M-Mrk/BlitzPong/pcb/controller/power.kicad_sch

## KiCad design pcb/controller/power.kicad_sch (2026-06-27)

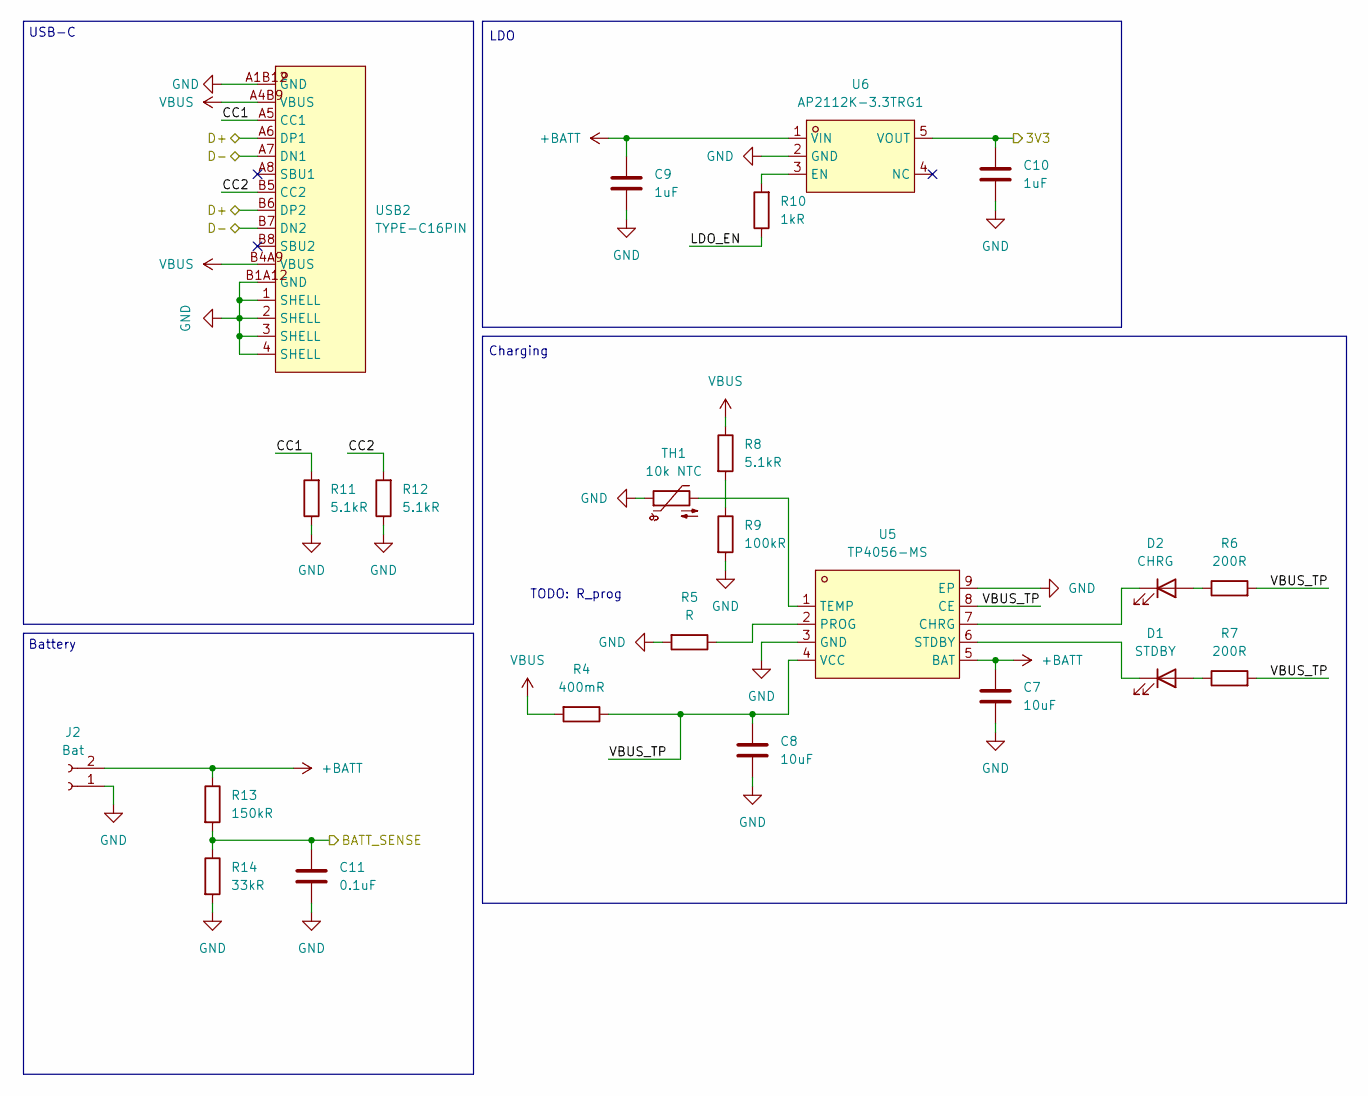
[picture p7: schematic power.kicad_sch]

Parts:
C7, C8: 10uF
C9, C10: 1uF
C11: 0.1uF
D1: STDBY; LED_0603_1608Metric; LCSC Part C51933293
D2: CHRG; LED_0603_1608Metric; LCSC Part C19712529
J2: Bat
R4: 400mR; R_2512_6332Metric; LCSC Part C49164929
R5: R
R6, R7: 200R
R8, R11, R12: 5.1kR
R9: 100kR
R10: 1kR
R13: 150kR
R14: 33kR
TH1: 10k NTC; SolderWire-0.1sqmm_1x02_P3.6mm_D0.4mm_OD1mm; LCSC Part C52204608
U5: TP4056-MS; SOP-8_L4.9-W3.9-P1.27-LS6.0-TL-EP; MPN TP4056-MS; LCSC Part C7473158
U6: AP2112K-3.3TRG1; SOT-23-5_L2.9-W1.6-P0.95-LS2.7-BR; MPN AP2112K-3.3TRG1(MS); LCSC Part C22365427
USB2: TYPE-C16PIN; USB-C-SMD_TYPE-C16PIN; MPN TYPE-C16PIN; LCSC Part C393939

Connections:
3V3: C10.1, U6.5 (VOUT)
+BATT: C7.1, C9.1, J2.2, R13.1, U5.5 (BAT), U6.1 (VIN)
BATT_SENSE: C11.1, R13.2, R14.1
CC1: R11.2, USB2.A5 (CC1)
CC2: R12.2, USB2.B5 (CC2)
D+: USB2.A6 (DP1), USB2.B6 (DP2)
D-: USB2.A7 (DN1), USB2.B7 (DN2)
GND: C7.2, C8.2, C9.2, C10.2, C11.2, J2.1, R5.2, R9.2, R11.1, R12.1, R14.2, TH1.1, U5.3 (GND), U5.9 (EP), U6.2 (GND), USB2.1 (SHELL), USB2.2 (SHELL), USB2.3 (SHELL), USB2.4 (SHELL), USB2.A1B12 (GND), USB2.B1A12 (GND)
LDO_EN: R10.1
unnamed: D1.1 (K), U5.6 (STDBY)
unnamed: D1.2 (A), R7.1
unnamed: D2.1 (K), U5.7 (CHRG)
unnamed: D2.2 (A), R6.1
unnamed: R5.1, U5.2 (PROG)
unnamed: R8.2, R9.1
unnamed: R10.2, U6.3 (EN)
unnamed: TH1.2, U5.1 (TEMP)
VBUS: R4.2, R8.1, USB2.A4B9 (VBUS), USB2.B4A9 (VBUS)
VBUS_TP: C8.1, R4.1, R6.2, R7.2, U5.4 (VCC), U5.8 (CE)

Notes on the sheet:
TODO: R_prog
Battery
Charging
USB-C
LDO
