M-Mrk/BlitzPong/pcb/controller/segment_display.kicad_sch

## KiCad design pcb/controller/segment_display.kicad_sch (2026-06-27)

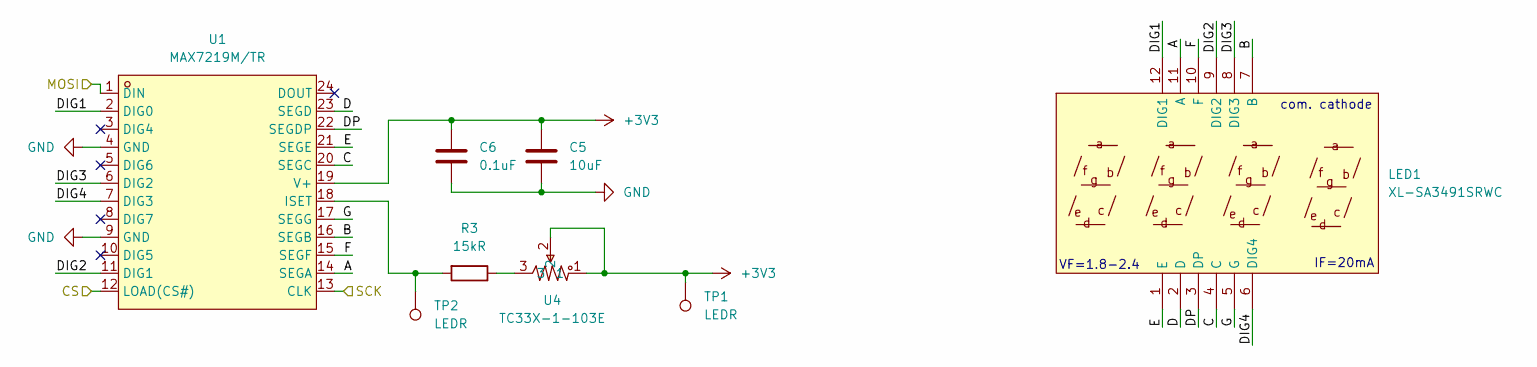
[picture p8: schematic segment_display.kicad_sch]

Parts:
C5: 10uF
C6: 0.1uF
LED1: XL-SA3491SRWC; LED-SEG-SMD_12P-P2.24_L39.4-W15.0_XL-SA3491SRWC; MPN XL-SA3491SRWC; LCSC Part C49652879
R3: 15kR
TP1, TP2: LEDR
U1: MAX7219M/TR; SOP-24_L15.4-W7.5-P1.27-LS10.4-BL; MPN MAX7219M/TR; LCSC Part C6705351
U4: TC33X-1-103E; RES-ADJ-SMD_3P-L3.8-W3.0-P2.00-BL-FS; MPN TC33X-1-103E; LCSC Part C911365

Connections:
+3V3: C5.1, C6.1, TP1.1, U1.19 (V+), U4.1, U4.2
A: LED1.11 (A), U1.14 (SEGA)
B: LED1.7 (B), U1.16 (SEGB)
C: LED1.4 (C), U1.20 (SEGC)
CS: U1.12 (LOAD(CS#))
D: LED1.2 (D), U1.23 (SEGD)
DIG1: LED1.12 (DIG1), U1.2 (DIG0)
DIG2: LED1.9 (DIG2), U1.11 (DIG1)
DIG3: LED1.8 (DIG3), U1.6 (DIG2)
DIG4: LED1.6 (DIG4), U1.7 (DIG3)
DP: LED1.3 (DP), U1.22 (SEGDP)
E: LED1.1 (E), U1.21 (SEGE)
F: LED1.10 (F), U1.15 (SEGF)
G: LED1.5 (G), U1.17 (SEGG)
GND: C5.2, C6.2, U1.4 (GND), U1.9 (GND)
MOSI: U1.1 (DIN)
unnamed: R3.1, U4.3
unnamed: R3.2, TP2.1, U1.18 (ISET)
SCK: U1.13 (CLK)

Notes on the sheet:
com. cathode
IF=20mA
VF=1.8-2.4
